paul999/pi-low-pass/3d/main_low_pass.bmp

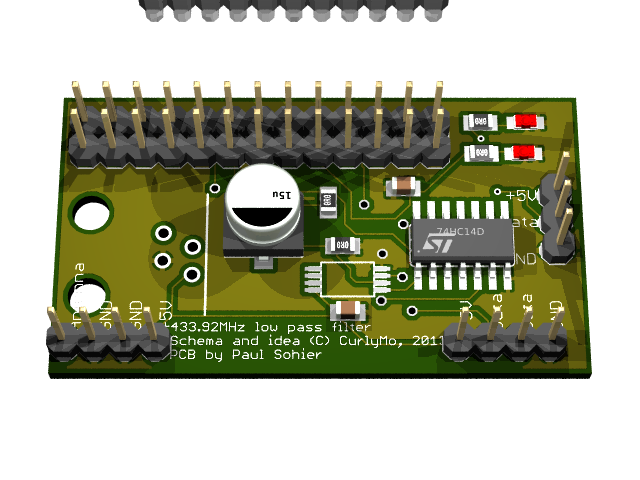
3d/main_low_pass.bmp
